Yaeltex/Kilomux-shield/PCB/v2/IMG serigrafia/595 1.bmp

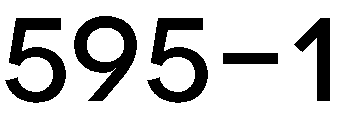
PCB/v2/IMG serigrafia/595 1.bmp
