Yaeltex/Kilomux-shield/PCB/v2/IMG serigrafia/595 2.bmp

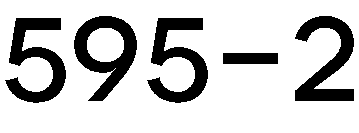
PCB/v2/IMG serigrafia/595 2.bmp
